venice1200/MiSTer_SNAC2IEC/Pictures/PCB_Bottom_SMD_v1.1.png

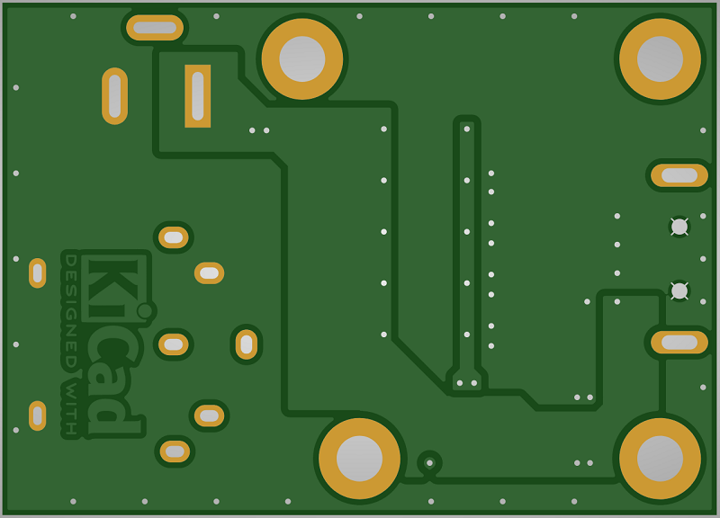
Pictures/PCB_Bottom_SMD_v1.1.png
